mstratman/fv1-pedal-platform/arduino/fv1-platform/euphorigenic14pt7b.h

const uint8_t euphorigenic14pt7bBitmaps[] PROGMEM = {
  0x00, 0x6F, 0xFF, 0x66, 0x66, 0x66, 0x62, 0x22, 0x00, 0x6F, 0xF6, 0x63,
  0x7B, 0xFD, 0xEC, 0x66, 0x33, 0x18, 0x0C, 0x60, 0xC4, 0x0C, 0x40, 0x84,
  0x08, 0xC0, 0x8C, 0x7F, 0xF1, 0x88, 0x18, 0x81, 0x08, 0x11, 0x81, 0x18,
  0x11, 0x8F, 0xFE, 0x31, 0x02, 0x10, 0x23, 0x02, 0x30, 0x23, 0x06, 0x20,
  0x0C, 0x01, 0x00, 0x40, 0x10, 0x0C, 0x8F, 0xE7, 0x59, 0xD2, 0x74, 0x1F,
  0x03, 0xF0, 0x3E, 0x07, 0xC1, 0x7C, 0x5D, 0x9E, 0x3F, 0x01, 0x00, 0x40,
  0x10, 0x78, 0x07, 0xCC, 0x06, 0xCC, 0x0C, 0xCC, 0x0C, 0xCC, 0x18, 0xCC,
  0x30, 0xCC, 0x30, 0xCC, 0x60, 0xCC, 0x40, 0x78, 0xDE, 0x01, 0xB3, 0x01,
  0x33, 0x03, 0x33, 0x06, 0x33, 0x06, 0x33, 0x0C, 0x33, 0x18, 0x33, 0x18,
  0x33, 0x30, 0x33, 0x70, 0x1E, 0x1E, 0x01, 0x30, 0x33, 0x03, 0x30, 0x33,
  0x03, 0x30, 0x33, 0x01, 0xE0, 0x1C, 0x03, 0xC0, 0x7C, 0x07, 0xE0, 0x76,
  0x0E, 0x30, 0xE3, 0x06, 0x18, 0x60, 0xC7, 0x0E, 0x39, 0x31, 0xE1, 0x6F,
  0xF6, 0x66, 0x19, 0xD9, 0xCC, 0x63, 0x18, 0xC6, 0x31, 0x8C, 0x63, 0x18,
  0xC6, 0x31, 0x8C, 0x63, 0x18, 0x63, 0x0E, 0x30, 0xC7, 0x0C, 0x63, 0x8C,
  0x63, 0x18, 0xC6, 0x31, 0x8C, 0x63, 0x18, 0xC6, 0x31, 0x8C, 0x67, 0x31,
  0xB9, 0x80, 0x1C, 0x0E, 0x37, 0x7D, 0x77, 0xF0, 0x41, 0xFD, 0xD7, 0xDD,
  0x8E, 0x07, 0x00, 0x06, 0x00, 0xC0, 0x18, 0x03, 0x0F, 0xFE, 0x0C, 0x01,
  0x80, 0x30, 0x06, 0x00, 0xC0, 0x6F, 0xF6, 0x24, 0xFC, 0x6F, 0xF6, 0x06,
  0x0C, 0x18, 0x30, 0x41, 0x83, 0x06, 0x08, 0x10, 0x60, 0xC1, 0x82, 0x04,
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
  {   776,   8,  25,  10,    1,  -19 },   // 0x46 'F'
  {   801,  12,  25,  14,    1,  -19 },   // 0x47 'G'
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

const GFXfont euphorigenic14pt7b PROGMEM = {
  (uint8_t  *)euphorigenic14pt7bBitmaps,
  (GFXglyph *)euphorigenic14pt7bGlyphs,
  0x20, 0x7E, 33 };

// Approx. 2943 bytes
