mstratman/fv1-pedal-platform/arduino/fv1-platform/Optima9pt7b.h

const uint8_t Optima9pt7bBitmaps[] PROGMEM = {
  0x00, 0xFF, 0xFA, 0x83, 0xC0, 0x99, 0x99, 0x90, 0x12, 0x14, 0x3F, 0x7E,
  0x24, 0x24, 0x28, 0x28, 0x7C, 0xFC, 0x48, 0x50, 0x10, 0x79, 0x56, 0x8D,
  0x1A, 0x1C, 0x1E, 0x1E, 0x2C, 0x58, 0xB9, 0x5F, 0x04, 0x08, 0x78, 0x21,
  0x98, 0x83, 0x31, 0x06, 0x64, 0x0C, 0xC8, 0x06, 0x20, 0x00, 0x4E, 0x01,
  0x22, 0x02, 0xC6, 0x09, 0x8C, 0x13, 0x18, 0x46, 0x30, 0x87, 0x80, 0x1C,
  0x08, 0x82, 0x20, 0x88, 0x34, 0x06, 0x03, 0x85, 0x31, 0xC6, 0xB0, 0xEC,
  0x33, 0x8E, 0x7C, 0xC0, 0xF8, 0x29, 0x49, 0x24, 0x92, 0x44, 0x88, 0x91,
  0x22, 0x49, 0x24, 0xA4, 0xA0, 0x22, 0x86, 0x8C, 0xEC, 0x82, 0x00, 0x08,
  0x04, 0x02, 0x01, 0x00, 0x87, 0xFC, 0x20, 0x10, 0x08, 0x04, 0x00, 0x5A,
  0x80, 0xF0, 0xF0, 0x08, 0x44, 0x21, 0x10, 0x84, 0x42, 0x21, 0x08, 0x00,
  0x3E, 0x31, 0x90, 0x58, 0x3C, 0x1E, 0x0F, 0x07, 0x83, 0xC1, 0xE0, 0xD0,
  0x4C, 0x63, 0xE0, 0x09, 0xD6, 0x31, 0x8C, 0x63, 0x18, 0xC6, 0x31, 0x80,
  0x3E, 0x47, 0x43, 0x03, 0x03, 0x03, 0x06, 0x04, 0x08, 0x10, 0x20, 0x40,
  0x7F, 0x7D, 0x0C, 0x18, 0x30, 0x61, 0x8C, 0x06, 0x06, 0x0C, 0x18, 0x6F,
  0x80, 0x03, 0x00, 0xC0, 0xF0, 0x2C, 0x13, 0x08, 0xC2, 0x31, 0x0C, 0x7F,
  0xC0, 0xC0, 0x30, 0x0C, 0x03, 0x00, 0x7E, 0x81, 0x02, 0x04, 0x0F, 0x03,
  0x03, 0x06, 0x0C, 0x18, 0x6F, 0x80, 0x1C, 0x20, 0x60, 0x40, 0xC0, 0xDC,
  0xE6, 0xC3, 0xC3, 0xC3, 0xC3, 0x66, 0x3C, 0xFE, 0x04, 0x10, 0x20, 0x81,
  0x04, 0x10, 0x20, 0x81, 0x04, 0x00, 0x3C, 0xC3, 0xC3, 0xC3, 0x42, 0x3C,
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
  {   389,   7,  13,  10,    2,  -12 },   // 0x46 'F'
  {   401,  12,  13,  14,    1,  -12 },   // 0x47 'G'
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

const GFXfont Optima9pt7b PROGMEM = {
  (uint8_t  *)Optima9pt7bBitmaps,
  (GFXglyph *)Optima9pt7bGlyphs,
  0x20, 0x7E, 21 };

// Approx. 1728 bytes
